The-Automation-Warehouse/The-Tesseract/code/src/effects/drawText.h

/**
 * @file drawText.h
 * @brief Header file for the drawText effect.
 * 
 * Creates a funtion that prints a text to the cube one letter after another with a travelling effect.
 */


#ifndef DRAWTEXT_H
#define DRAWTEXT_H

#include <Arduino.h>
#define FastLED_INTERNAL
#include <FastLED.h>
#include "../tesseractFunctions.h"



#define NUM_LEDS 1000
#define NUM_LAYERS 10


uint8_t DIGIT_0[10][10] = {
    {0, 0, 0, 0, 0, 0, 0, 0, 0, 0},
    {0, 0, 0, 1, 1, 1, 1, 0, 0, 0},
    {0, 0, 1, 0, 0, 0, 0, 1, 0, 0},
    {0, 0, 1, 0, 0, 0, 0, 1, 0, 0},
    {0, 0, 1, 0, 0, 0, 0, 1, 0, 0},
    {0, 0, 1, 0, 0, 0, 0, 1, 0, 0},
    {0, 0, 1, 0, 0, 0, 0, 1, 0, 0},
    {0, 0, 1, 0, 0, 0, 0, 1, 0, 0},
    {0, 0, 0, 1, 1, 1, 1, 0, 0, 0},
    {0, 0, 0, 0, 0, 0, 0, 0, 0, 0}
};

#include <stdint.h>

uint8_t DIGIT_1[10][10] = {
    {0, 0, 0, 0, 0, 0, 0, 0, 0, 0},
    {0, 0, 0, 0, 0, 1, 0, 0, 0, 0},
    {0, 0, 0, 0, 1, 1, 0, 0, 0, 0},
    {0, 0, 0, 1, 0, 1, 0, 0, 0, 0},
    {0, 0, 0, 0, 0, 1, 0, 0, 0, 0},
    {0, 0, 0, 0, 0, 1, 0, 0, 0, 0},
    {0, 0, 0, 0, 0, 1, 0, 0, 0, 0},
    {0, 0, 0, 0, 0, 1, 0, 0, 0, 0},
    {0, 0, 0, 0, 1, 1, 1, 0, 0, 0},
    {0, 0, 0, 0, 0, 0, 0, 0, 0, 0}
};


uint8_t DIGIT_2[10][10] = {
    {0, 0, 0, 0, 0, 0, 0, 0, 0, 0},
    {0, 0, 0, 0, 1, 1, 0, 0, 0, 0},
    {0, 0, 0, 1, 0, 0, 1, 0, 0, 0},
    {0, 0, 0, 0, 0, 0, 1, 0, 0, 0},
    {0, 0, 0, 0, 0, 0, 1, 0, 0, 0},
    {0, 0, 0, 0, 0, 1, 0, 0, 0, 0},
    {0, 0, 0, 0, 1, 0, 0, 0, 0, 0},
    {0, 0, 0, 1, 0, 0, 0, 0, 0, 0},
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
    {0, 0, 1, 0, 0, 0, 0, 1, 0, 0},
    {0, 0, 0, 1, 0, 0, 1, 0, 0, 0},
    {0, 0, 0, 0, 1, 1, 0, 0, 0, 0},
    {0, 0, 0, 0, 1, 1, 0, 0, 0, 0},
    {0, 0, 0, 1, 0, 0, 1, 0, 0, 0},
    {0, 0, 1, 0, 0, 0, 0, 1, 0, 0},
    {0, 0, 1, 0, 0, 0, 0, 1, 0, 0},
    {0, 0, 0, 0, 0, 0, 0, 0, 0, 0}
};


uint8_t LETTER_Y[10][10] = {
    {0, 0, 0, 0, 0, 0, 0, 0, 0, 0},
    {0, 1, 0, 0, 0, 0, 0, 1, 0, 0},
    {0, 0, 1, 0, 0, 0, 1, 0, 0, 0},
    {0, 0, 0, 1, 0, 1, 0, 0, 0, 0},
    {0, 0, 0, 0, 1, 0, 0, 0, 0, 0},
    {0, 0, 0, 0, 1, 0, 0, 0, 0, 0},
    {0, 0, 0, 0, 1, 0, 0, 0, 0, 0},
    {0, 0, 0, 0, 1, 0, 0, 0, 0, 0},
    {0, 0, 0, 0, 1, 0, 0, 0, 0, 0},
    {0, 0, 0, 0, 0, 0, 0, 0, 0, 0}
};

uint8_t LETTER_Z[10][10] = {
    {0, 0, 0, 0, 0, 0, 0, 0, 0, 0},
    {0, 0, 1, 1, 1, 1, 1, 1, 0, 0},
    {0, 0, 0, 0, 0, 0, 0, 1, 0, 0},
    {0, 0, 0, 0, 0, 0, 1, 0, 0, 0},
    {0, 0, 0, 0, 0, 1, 0, 0, 0, 0},
    {0, 0, 0, 0, 1, 0, 0, 0, 0, 0},
    {0, 0, 0, 1, 0, 0, 0, 0, 0, 0},
    {0, 0, 1, 0, 0, 0, 0, 0, 0, 0},
    {0, 0, 1, 1, 1, 1, 1, 1, 0, 0},
    {0, 0, 0, 0, 0, 0, 0, 0, 0, 0}
};

uint8_t CHAR_COLON[10][10] = {
    {0, 0, 0, 0, 0, 0, 0, 0, 0, 0},
    {0, 0, 0, 0, 1, 1, 0, 0, 0, 0},
    {0, 0, 0, 0, 1, 1, 0, 0, 0, 0},
    {0, 0, 0, 0, 0, 0, 0, 0, 0, 0},
    {0, 0, 0, 0, 0, 0, 0, 0, 0, 0},
    {0, 0, 0, 0, 0, 0, 0, 0, 0, 0},
    {0, 0, 0, 0, 0, 0, 0, 0, 0, 0},
    {0, 0, 0, 0, 1, 1, 0, 0, 0, 0},
    {0, 0, 0, 0, 1, 1, 0, 0, 0, 0},
    {0, 0, 0, 0, 0, 0, 0, 0, 0, 0}
};


uint8_t (*LETTERS[37])[10][10] = {
    &DIGIT_0,
    &DIGIT_1,
    &DIGIT_2,
    &DIGIT_3,
    &DIGIT_4,
    &DIGIT_5,
    &DIGIT_6,
    &DIGIT_7,
    &DIGIT_8,
    &DIGIT_9,
    &LETTER_A,
    &LETTER_B,
    &LETTER_C,
    &LETTER_D,
    &LETTER_E,
    &LETTER_F,
    &LETTER_G,
    &LETTER_H,
    &LETTER_I,
    &LETTER_J,
    &LETTER_K,
    &LETTER_L,
    &LETTER_M,
    &LETTER_N,
    &LETTER_O,
    &LETTER_P,
    &LETTER_Q,
    &LETTER_R,
    &LETTER_S,
    &LETTER_T,
    &LETTER_U,
    &LETTER_V,
    &LETTER_W,
    &LETTER_X,
    &LETTER_Y,
    &LETTER_Z,
    &CHAR_COLON
};


//draw the text to the cube one letter after another with a travelling effect 
void drawText(CRGB pixels[NUM_LEDS], String text, uint8_t initialHue, uint8_t deltaHue, int delayTime) {
    //use the setLed function to draw the text
    //each letter starts in the back and moves to the front
    //when it reaches the front, the next letter starts

    FastLED.setBrightness(255);
    
    int currentLetterIndex = 0;
    int currentLetterMatixIndex = 0;
    char currentLetter = text[currentLetterIndex];

    if (currentLetter >= 48 && currentLetter <= 57) {
        currentLetterMatixIndex = int(currentLetter) - 48;
    }
    else if (currentLetter >= 65 && currentLetter <= 90) {
        currentLetterMatixIndex = int(currentLetter) - 65 + 10;
    }
    else if (currentLetter == ':') {
        currentLetterMatixIndex = 36; // index of CHAR_COLON in LETTERS array
    }

    

    for (unsigned int i = 0; i < text.length(); i++) {
        for (int y = 9; y > -1; y--) {
            for (int x = 9; x > -1; x--) {
                for (int z = 0; z < 10; z++) {
                    if ((*LETTERS[currentLetterMatixIndex])[9 - z][x] == 1) {
                        setLed(x, y, z, CHSV(initialHue, 255, 255));
                    }     
                }
            }

            fadeToBlackBy(pixels, NUM_LEDS, 100);
            
            FastLED.show();
            delay(delayTime);
            
        }
        initialHue += deltaHue;
        currentLetterIndex++;
        currentLetter = text[currentLetterIndex];
        if (currentLetter >= 48 && currentLetter <= 57) {
            currentLetterMatixIndex = int(currentLetter) - 48;
        }
        else {
            currentLetterMatixIndex = int(currentLetter) - 65 + 10;
        }
    }

    unsigned long startMillis = millis();
    while (millis() - startMillis < 500) {
        
        fadeToBlackBy(pixels, NUM_LEDS, 100);
        FastLED.show();
    }


}




#endif // DRAWTEXT_H
