The-Automation-Warehouse/The-Tesseract/code/src/images.h

/**
 * @file images.h
 * @brief Header file for the images.
 * 
 * Contains the images for the tesseract.
 */


#ifndef IMAGES_H
#define IMAGES_H

#include <Arduino.h>


const PROGMEM uint16_t debug_icon [50*50] = {
0x9ad6, 0x9ad6, 0x9ad6, 0x9ad6, 0x9ad6, 0x9ad6, 0x9ad6, 0x9ad6, 0x9ad6, 0x9ad6, 0x9ad6, 0x9ad6, 0x9ad6, 0x9ad6, 0x9ad6, 0x9ad6, 0x9ad6, 0x9ad6, 0x9ad6, 0x9ad6, 0x9ad6, 0x9ad6, 0x9ad6, 0x9ad6, 0x9ad6, 0x9ad6, 0x9ad6, 0x9ad6, 0x9ad6, 0x9ad6, 0x9ad6, 0x9ad6, 0x9ad6, 0x9ad6, 0x9ad6, 0x9ad6, 0x9ad6, 0x9ad6, 0x9ad6, 0x9ad6, 0x9ad6, 0x9ad6, 0x9ad6, 0x9ad6, 0x9ad6, 0x9ad6, 0x9ad6, 0x9ad6, 0x9ad6, 0x9ad6, 
0x9ad6, 0x9ad6, 0x9ad6, 0x9ad6, 0x9ad6, 0x9ad6, 0x9ad6, 0x9ad6, 0x9ad6, 0x9ad6, 0x9ad6, 0x9ad6, 0x9ad6, 0x9ad6, 0x9ad6, 0x9ad6, 0x9ad6, 0x9ad6, 0x9ad6, 0x9ad6, 0x9ad6, 0x9ad6, 0x9ad6, 0x9ad6, 0x9ad6, 0x9ad6, 0x9ad6, 0x9ad6, 0x9ad6, 0x9ad6, 0x9ad6, 0x9ad6, 0x9ad6, 0x9ad6, 0x9ad6, 0x9ad6, 0x9ad6, 0x9ad6, 0x9ad6, 0x9ad6, 0x9ad6, 0x9ad6, 0x9ad6, 0x9ad6, 0x9ad6, 0x9ad6, 0x9ad6, 0x9ad6, 0x9ad6, 0x9ad6, 
0x9ad6, 0x9ad6, 0x9ad6, 0x9ad6, 0x9ad6, 0x9ad6, 0x9ad6, 0x9ad6, 0x9ad6, 0x9ad6, 0x9ad6, 0x9ad6, 0x9ad6, 0x9ad6, 0x9ad6, 0x9ad6, 0x9ad6, 0x9ad6, 0x9ad6, 0x9ad6, 0x9ad6, 0x9ad6, 0x9ad6, 0x9ad6, 0x9ad6, 0x9ad6, 0x9ad6, 0x9ad6, 0x9ad6, 0x9ad6, 0x9ad6, 0x9ad6, 0x9ad6, 0x9ad6, 0x9ad6, 0x9ad6, 0x9ad6, 0x9ad6, 0x9ad6, 0x9ad6, 0x9ad6, 0x9ad6, 0x9ad6, 0x9ad6, 0x9ad6, 0x9ad6, 0x9ad6, 0x9ad6, 0x9ad6, 0x9ad6, 
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
};


#endif // IMAGES_H
