The-Automation-Warehouse/The-Tesseract/code/src/effects/effects.h

/**
 * @file effects.h
 * @brief Header file for all of the effects.
 * 
 * Includes all of the effects for the Tesseract.
 */


#ifndef EFFECTS_H
#define EFFECTS_H

#include <Arduino.h>
#include "clock.h"
#include "drawText.h"
#include "fillCube.h"
#include "lines.h"
#include "planets.h"
#include "simpleRainbow.h"
#include "sparkles.h"
#include "spectrumAnalyser.h"
#include "tesseract.h"
#include "tetris.h"
#include "vortex.h"


#endif // EFFECTS_H
